MarveyHAB/Projektarbeit-Sunflower/Funktionen/drehen.py

from machine    import Pin, I2C #i2c löschen
from time       import sleep_us,sleep,sleep_ms
from Sonne      import getAZ

ini_grund_pos	= Pin(21 , Pin.IN,Pin.PULL_UP)
rechts			= Pin(27 , Pin.IN,Pin.PULL_UP)
links			= Pin(26 , Pin.IN,Pin.PULL_UP)

brake			= Pin(11 , Pin.OUT,value = 0)
# Pins für den DRV8825 Schrittmotor-Treiber
DIR_PIN   = Pin(2, Pin.OUT,value =0)  # Richtungs-Pin 1 Uhrzeigersinn
STEP_PIN  = Pin(3, Pin.OUT,value =0)  
SLEEP_PIN = Pin(4, Pin.OUT,value =0)  
PSU_24V   = Pin (12, Pin.OUT,value =0)

micro_step = 4 		#1/4
ratio      = 50		
time_step  = 2500 	#in us
grund_pos  = 180
ini_mitte  = 4

#Löschen
"""
from kompass import QMC5883L
i2c = I2C(0, scl=Pin(1), sda=Pin(0))
kompi =QMC5883L(i2c) 

from _thread	import allocate_lock
NOTHALT = allocate_lock()
"""
#ende löschen


def drehen_kali(NOTHALT):
    
    dif=0 #testen ob es sein muss
    if ini_grund_pos.value() == 0:
            print ("Ini Drehen Grundpos. angesprochen")
            with open("totale_pos.txt","r") as datei:
                inhalt  = datei.read()
                abs_pos = int(inhalt)
            if abs_pos != 180:
                with open("totale_pos.txt","w") as datei:
                    datei.write("180")
            return 0,180

    with open("totale_pos.txt","r") as datei:
        inhalt  = datei.read()
        abs_pos = int(inhalt)
    
    if abs_pos<180: #dann rechts fahren
        DIR_PIN.value(0) #im Uhrzeigersinn
        print("rechts rum")
        dif= 180-abs_pos
    
    if abs_pos>180: #dann links fahren
        DIR_PIN.value(1)
        print ("links rum")
        dif= abs_pos-180
    
    #print("Diff  %i" %dif)
    steps = round(((dif+5)/1.8)*micro_step*ratio)
    print("Steps: %i"%steps)
    
    PSU_24V.value(1)
    SLEEP_PIN.value(1)
    brake.value(1)
    sleep(.2)

    
    for _ in range(steps):
        if NOTHALT.locked()== True:
            break
        STEP_PIN.value(1)
        sleep_us(round(time_step/2))  # Wartezeit vor dem nächsten Schritt
        STEP_PIN.value(0)
        sleep_us(round(time_step/2))  # Wartezeit nach dem Schritt
        if ini_grund_pos.value() == 0:
            print ("Ini Drehen Grundpos. angesprochen")
            print("Fahre auf Ini Mitte")
            for _ in range(round(((ini_mitte)/1.8)*micro_step*ratio)):
                if NOTHALT.locked()== True:
                    break
                STEP_PIN.value(1)
                sleep_us(round(time_step/2))  # Wartezeit vor dem nächsten Schritt
                STEP_PIN.value(0)
                sleep_us(round(time_step/2))  # Wartezeit nach dem Schritt
            break
        
    sleep(.2)
    PSU_24V.value(0)
    SLEEP_PIN.value(0)
    brake.value(0)
        
    if NOTHALT.locked()== True:
        print("Not-Halt hat ausgelöst")
        return 41,999
    
    with open("totale_pos.txt","w") as datei:
        datei.write("180")
    
    if ini_grund_pos.value() == 0:
        return 0,180
    else:
        print("Muss im Handbetrieb angefahren werden, da er die pos. nicht findet.")
        return 30,180
        

def drehen_grundpos(NOTHALT):
    
    #aktuelle Position herausfinden
    with open("totale_pos.txt","r") as datei:
        inhalt  = datei.read()
        abs_pos = int(inhalt)
    akt_pos = abs_pos
    print("aktuelle Pos.:%i"%akt_pos)
    if akt_pos == grund_pos:
        print("aktuelle Pos. entspricht noch der Grundpos.")
        return 0
    
    # Berechnung des kürzesten Weges im Uhrzeigersinn
    im_uhrzeigersinn = (grund_pos - akt_pos) % 360
    # Berechnung des kürzesten Weges gegen den Uhrzeigersinn
    gegen_uhrzeigersinn = (akt_pos - grund_pos) % 360
    #was ist kürzer
    if im_uhrzeigersinn<gegen_uhrzeigersinn:
        DIR_PIN.value(0) #im Uhrzeigersinn
        print("im Uhrzeigersinn sind es %i grad"%im_uhrzeigersinn)
        dif=im_uhrzeigersinn
        if 360<akt_pos+dif:
            akt_pos=akt_pos-360+dif
        else:
            akt_pos=akt_pos+dif
    else:
        DIR_PIN.value(1) #gegen den Uhrzeigersinn
        print("gegen Uhrzeigersinn sind es %i grad"%gegen_uhrzeigersinn)
        dif=gegen_uhrzeigersinn
        if 0>akt_pos-dif:
            akt_pos=akt_pos+360-dif
        else:
            akt_pos=akt_pos-dif
    #+5° damit er den Ini auf jeden Fall erreicht, wenn nicht liegt vermutlich ein Fehler vor
    steps = round(((dif+5)/1.8)*micro_step*ratio)
    
    PSU_24V.value(1)
    SLEEP_PIN.value(1)
    brake.value(1)
    sleep(.2)

    
    gefahrene_steps = 0 #um zu zählen wie weit er gefahren ist vor Not aus
    
    for _ in range(steps):
        if NOTHALT.locked()== True:
            break
        gefahrene_steps +=1
        STEP_PIN.value(1)
        sleep_us(round(time_step/2))
        STEP_PIN.value(0)
        sleep_us(round(time_step/2))
        if ini_grund_pos.value() == 0:
            print ("Ini Drehen Grundpos. angesprochen")
            print("Fahre auf Ini Mitte")
            for _ in range(round(((ini_mitte)/1.8)*micro_step*ratio)):
                if NOTHALT.locked()== True:
                    break
                STEP_PIN.value(1)
                sleep_us(round(time_step/2))  # Wartezeit vor dem nächsten Schritt
                STEP_PIN.value(0)
                sleep_us(round(time_step/2))  # Wartezeit nach dem Schritt
            break

    brake.value(0)
    sleep(.2)
    SLEEP_PIN.value(0)
    PSU_24V.value(0)



    print("angefahrene Pos. %i"%akt_pos)
    with open("totale_pos.txt","w") as datei:
            datei.write(str(akt_pos))
    
    if ini_grund_pos.value() == 1:
        print("Ini Grundpos. wurde nicht erreicht")
        return 31
    
    return 0


def drehen_sonne(NOTHALT,kompass_az,akt_pos):
    
    sunPos = int(getAZ(51,7,2))#aktuelle Sonnenposition abfragen
    #sunPos=90
    print("Sonnenposition: %i"%sunPos)
    
    with open("totale_pos.txt","r") as datei:#Absolute Position auslesen
        inhalt  = datei.read()
        abs_pos = int(inhalt)
    
    print("absolute Pos.:%i"%abs_pos)
    print("Kompassausrichtung:%i"%kompass_az)
    if abs_pos == 180:
        akt_pos = kompass_az
    #das heißt beim ersten mal richtung Sonne ausrichten nimmt er Kompass als die aktuelle Position
    
    if akt_pos == sunPos:
        print("aktuelle Pos. entspricht noch der Sonnenpos.")
        return(0,akt_pos)
    
    if sunPos <= akt_pos+1 and sunPos >= akt_pos-1:
        print("Drehen steht noch +-1 in Sonnenposition")
        return(0,akt_pos)
    
    im_uhrzeigersinn    = (sunPos - akt_pos) % 360    # Berechnung des kürzesten Weges im Uhrzeigersinnn
    gegen_uhrzeigersinn = (akt_pos - sunPos) % 360    # Berechnung des kürzesten Weges gegen den Uhrzeigersinn
    
    if im_uhrzeigersinn < gegen_uhrzeigersinn:#was ist kürzer
        DIR_PIN.value(0) #im Uhrzeigersinn
        print("im Uhrzeigersinn sind es %i grad"%im_uhrzeigersinn)
        dif=im_uhrzeigersinn
    
    else:
        DIR_PIN.value(1) #gegen den Uhrzeigersinn
        print("gegen Uhrzeigersinn sind es %i grad"%gegen_uhrzeigersinn)
        dif=gegen_uhrzeigersinn
        
    
    PSU_24V.value(1)
    steps = round((dif/1.8)*micro_step*ratio)
    SLEEP_PIN.value(1)
    brake.value(1)
    sleep(.2)
    
    gemachte_steps = 0
    for _ in range(steps):
        if NOTHALT.locked()== True:
            break
        gemachte_steps += 1
        STEP_PIN.value(1)
        sleep_us(round(time_step/2))  # Wartezeit vor dem nächsten Schritt
        STEP_PIN.value(0)
        sleep_us(round(time_step/2))  # Wartezeit nach dem Schritt
    
    sleep(.2)
    brake.value(0)
    sleep(.2)
    SLEEP_PIN.value(0)
    PSU_24V.value(0)
    
    if NOTHALT.locked()== True:
        dif = round((1.8 * gemachte_steps) / (micro_step * ratio))
        print("So viel grad hat er vor Not-Aus gedreht: %i"%dif)
        print("wird in Absoluter Pos. gespeichert")
        if DIR_Pin.value()==1: #gegen den Uhrzeigersinn
            abs_pos = abs_pos-dif
        else:
            abs_pos = abs_pos+dif
            
        with open("totale_pos.txt","w") as datei:
            datei.write(str(abs_pos))
        print("Not-Halt hat ausgelöst")
        return 41,999    
    
    if DIR_PIN.value()==0:#im Uhrzeigersinn
        abs_pos = abs_pos+dif
        
        if 360 < akt_pos+dif:
            akt_pos=akt_pos-360+dif
        else:
            akt_pos=akt_pos+dif
    
    else:
        abs_pos = abs_pos-dif
        if 0 > akt_pos-dif:
            akt_pos=akt_pos+360-dif
        else:
            akt_pos=akt_pos-dif
    
    print("angefahrene Pos. %i"%akt_pos)
    print("absolute Pos. %i"%abs_pos)
    with open("totale_pos.txt","w") as datei:
            datei.write(str(abs_pos))

    return 0,akt_pos


def drehen_hand():
    
    while rechts.value()==1 or links.value()==1:

        first_run_rechts   = True
        schleife_rechts    = False
        first_run_links = True
        schleife_links  = False        

        #rechts Handbetrieb
        while rechts.value()==0 and links.value()==1:
            
            if first_run_rechts == True:
                first_run_rechts = False
                schleife_rechts = True
                DIR_PIN.value(1) 
                PSU_24V.value(1)
                brake.value(1)
                SLEEP_PIN.value(1)
                sleep(.2)
                
            STEP_PIN.value(1)
            sleep_us(round(time_step/2)) 
            STEP_PIN.value(0)
            sleep_us(round(time_step/2))
            
        if schleife_rechts == True:
            schleife_rechts = False
            sleep(.2)
            PSU_24V.value(0)
            brake.value(0)
            SLEEP_PIN.value(0)
            sleep(.2)
        
        #links Handbetrieb
        while links.value()==0 and rechts.value()==1:
            
            if first_run_links == True:
                first_run_links = False
                schleife_links = True
                DIR_PIN.value(0) 
                PSU_24V.value(1)
                brake.value(1)
                SLEEP_PIN.value(1)
                sleep(.2)
                
            STEP_PIN.value(1)
            sleep_us(round(time_step/2)) 
            STEP_PIN.value(0)
            sleep_us(round(time_step/2))
            
        if schleife_links == True:
            schleife_links = False
            sleep(.1)
            PSU_24V.value(0)
            brake.value(0)
            SLEEP_PIN.value(0)
            sleep(.2)
    return 0



#a=kompi.axesAverage(100)
#w=int(kompi.calcAngle(a[0],a[1]))

#drehen_kali(NOTHALT)
#sleep(2)
#drehen_sonne(NOTHALT,w,195)
#drehen_grundpos(NOTHALT)
#drehen_kali(NOTHALT)
#drehen_hand()
