MarveyHAB/Projektarbeit-Sunflower/Kalibrierung & Tests/Treiber Einstellen.py

from machine import Pin

Bremse = Pin(11 , Pin.OUT, value=0)
luefter = Pin(13 , Pin.OUT, value=0)
PSU24V = Pin(12 , Pin.OUT, value=0)
M1_sleep = Pin(4 , Pin.OUT, value=0)
M2_sleep = Pin(7 , Pin.OUT, value=0)
M3_sleep = Pin(10 , Pin.OUT, value=0)
